ranseyer/USBasp-IR-AddOn/HW/1.Mini/MiniAdd-OnV11.top.jpg

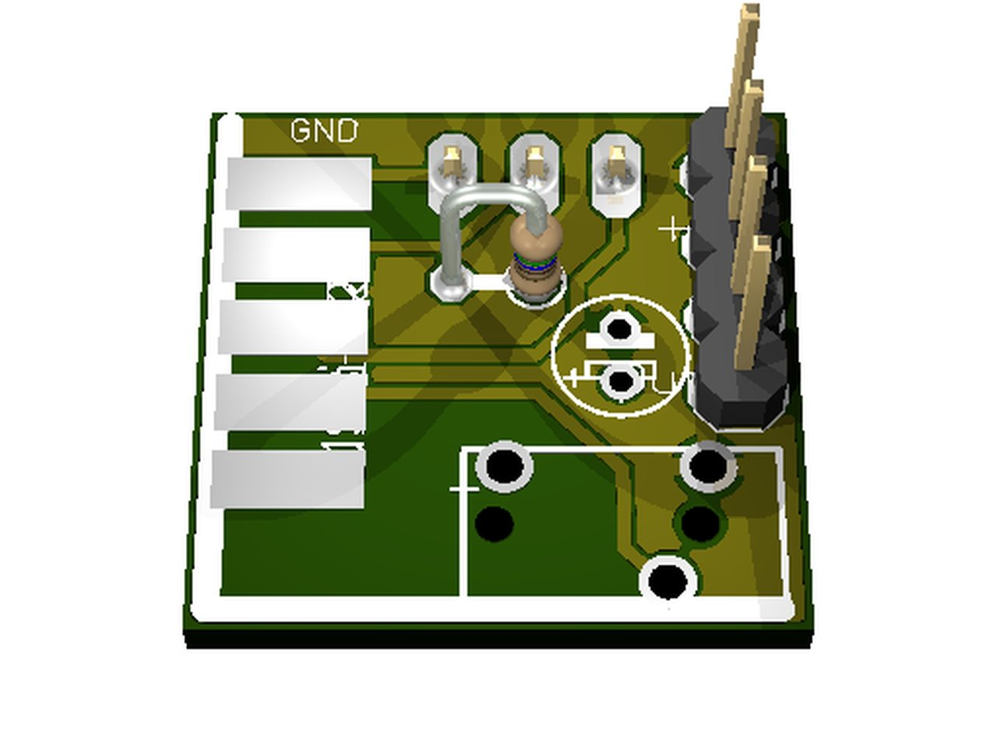
HW/1.Mini/MiniAdd-OnV11.top.jpg
