ranseyer/USBasp-IR-AddOn/HW/2.Medium/Add-OnV20-final.jpg

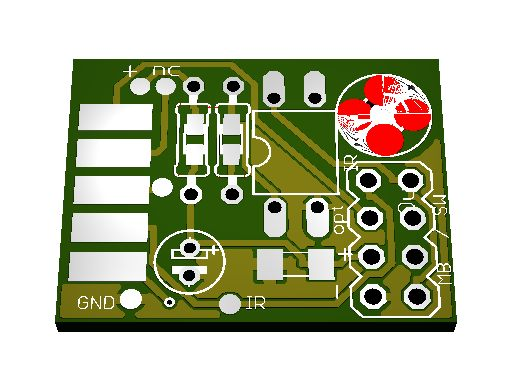
HW/2.Medium/Add-OnV20-final.jpg
