ranseyer/USBasp-IR-AddOn/HW/3.Large/Large-Board.png

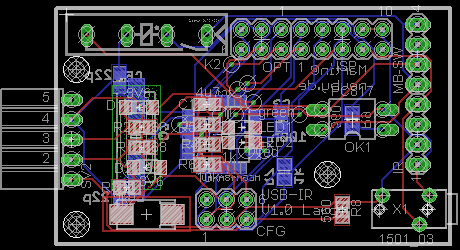
HW/3.Large/Large-Board.png
