ranseyer/USBasp-IR-AddOn/HW/3.Large/Large-Schem.png

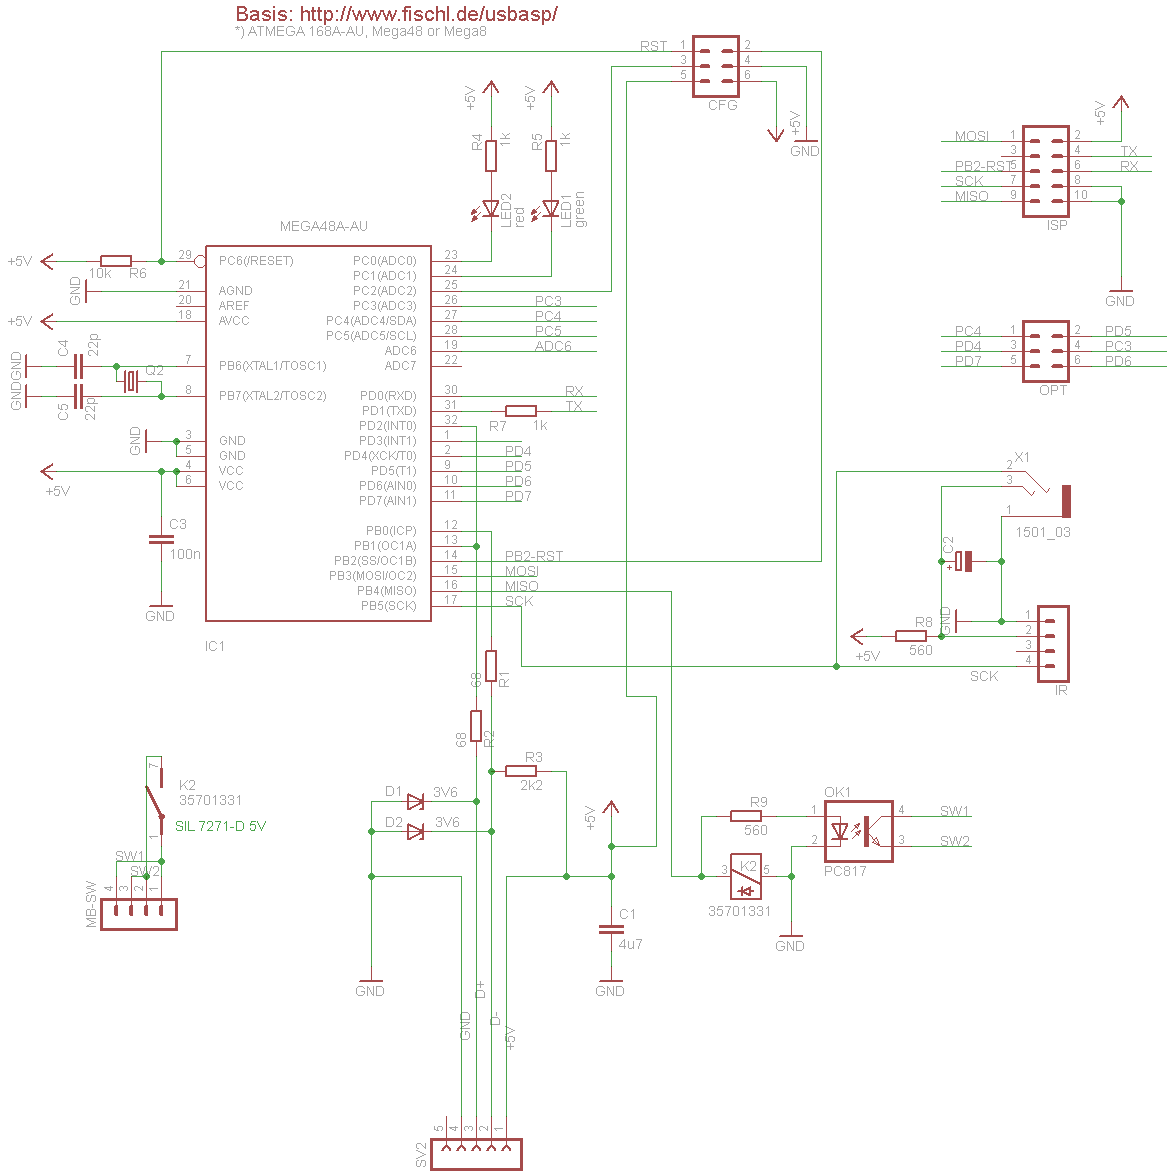
HW/3.Large/Large-Schem.png
