ranseyer/USBasp-IR-AddOn/HW/3.Large/UsbAsp_IR-Gross-41-bot.jpg

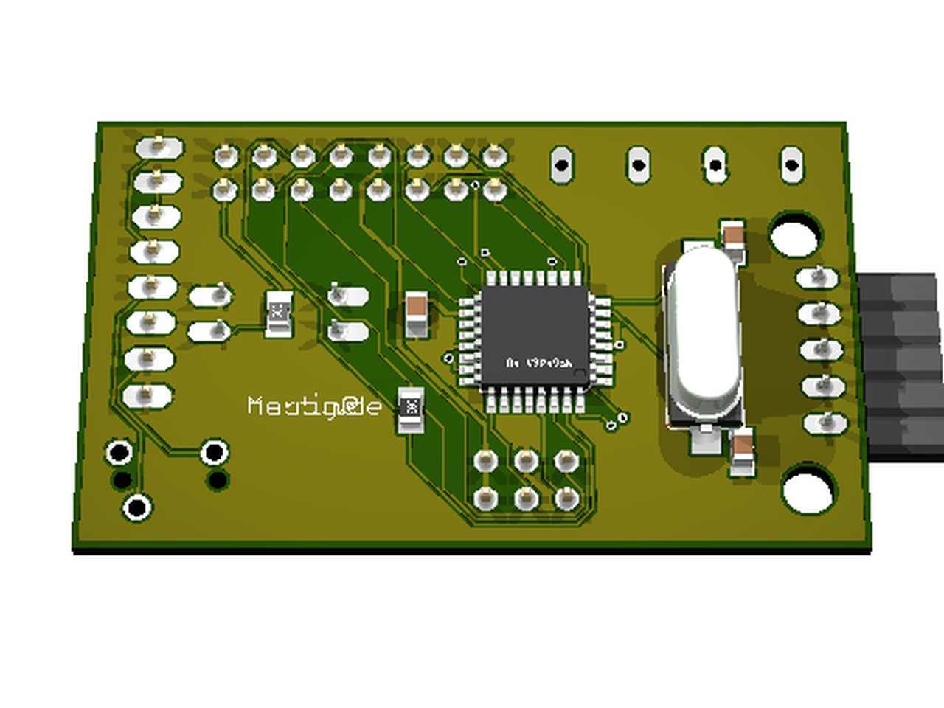
HW/3.Large/UsbAsp_IR-Gross-41-bot.jpg
